whbeers/noise_floor/schematics/noise_floor-v0.02.pdf

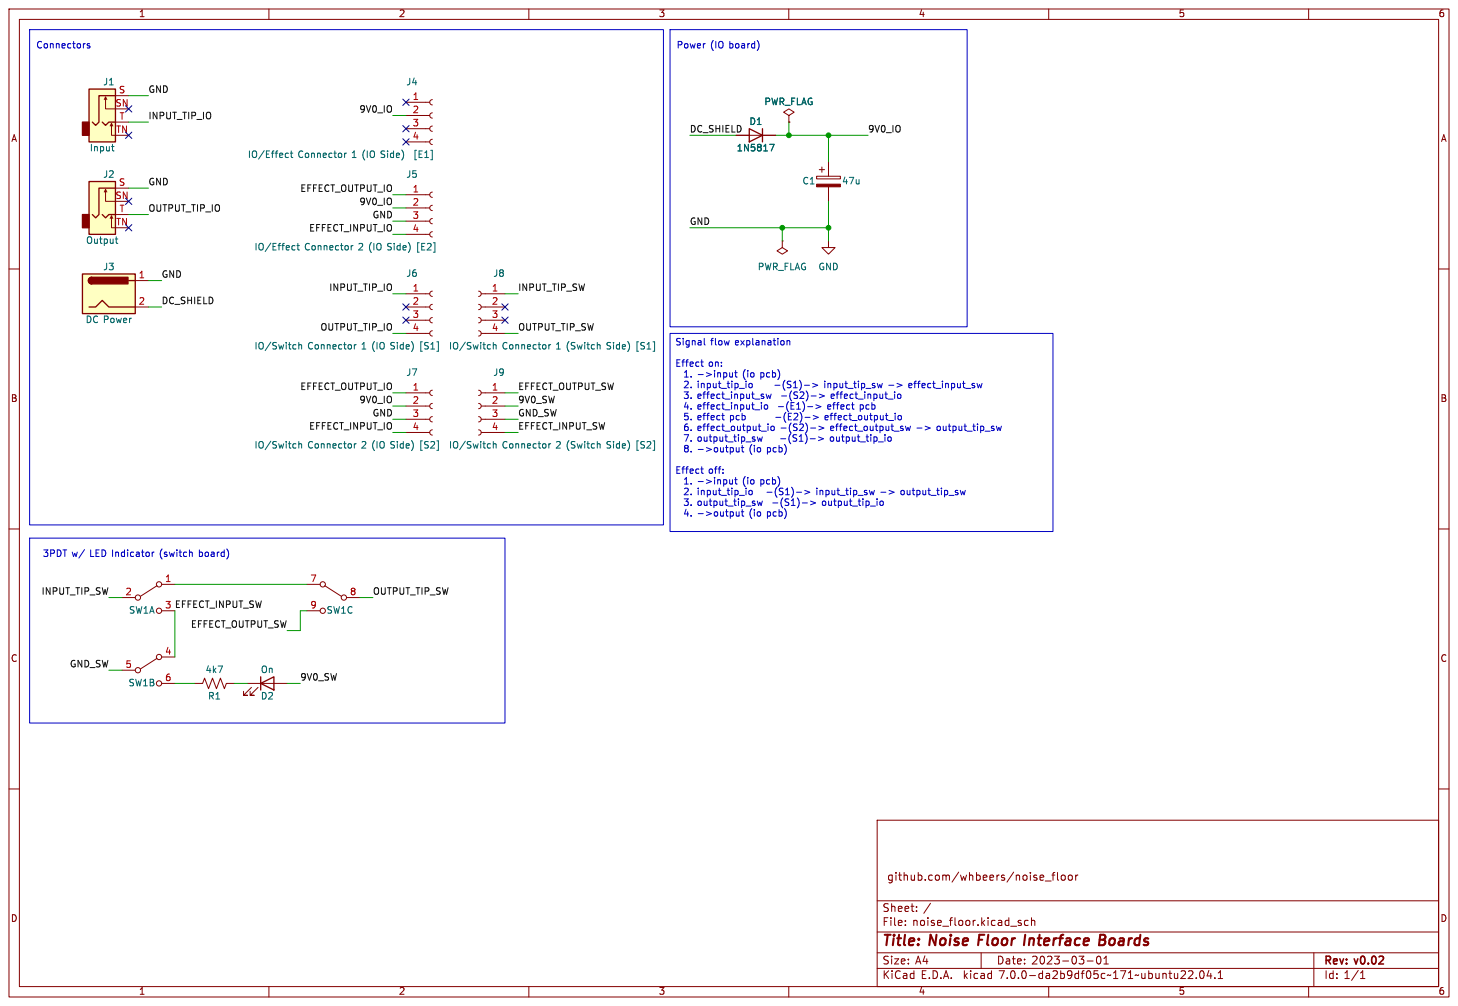
[picture p13: page 1]

File: noise_floor.kicad_sch Sheet: / github.com/whbeers/noise_floor R1

Id: 1/1 Title: Noise Floor Interface Boards
