whbeers/noise_floor/schematics/noise_floor-v0.01.pdf

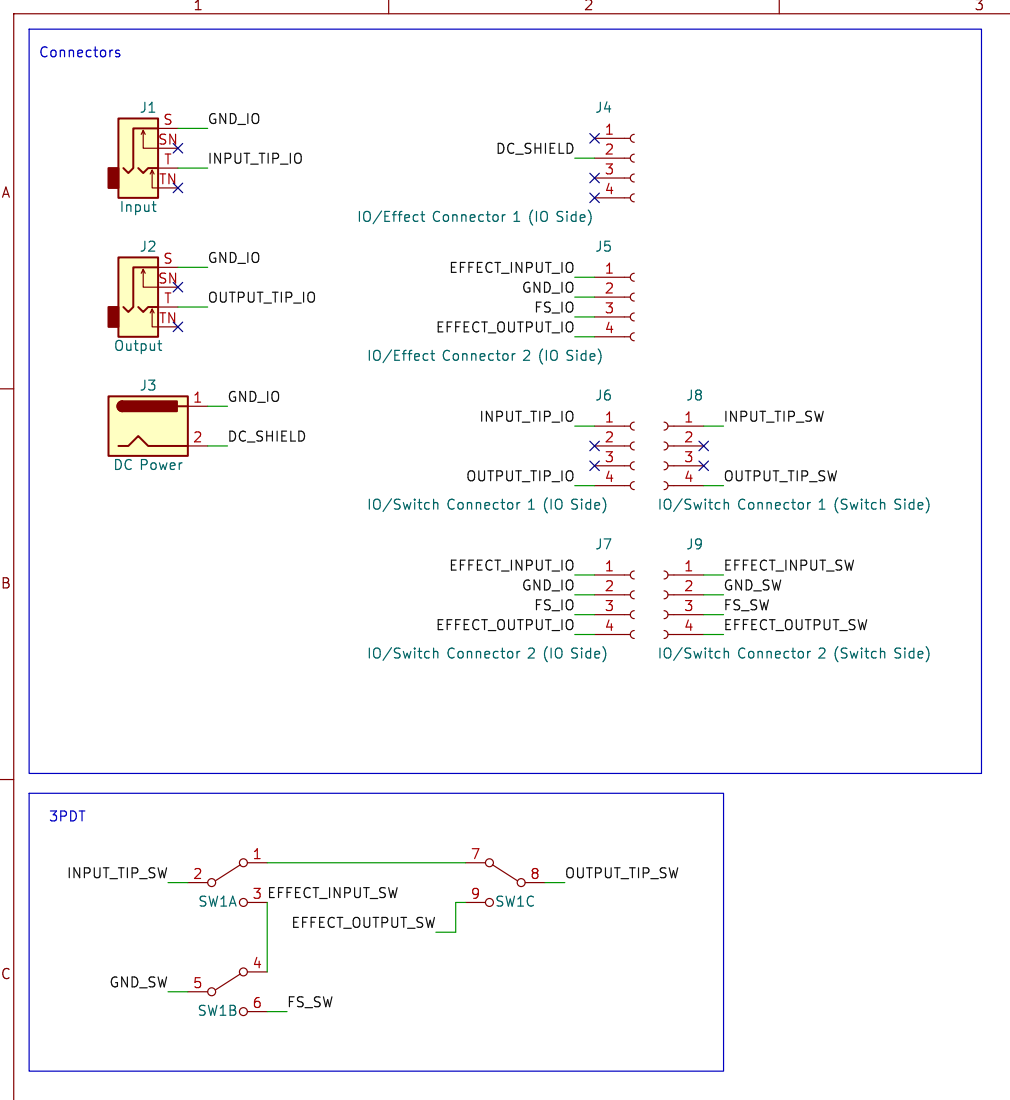
[picture p14: page 1]

File: noise_floor.kicad_sch Sheet: / github.com/whbeers/noise_floor

Id: 1/1 Title: Noise Floor Interface Boards
